Indivikar/mateCounter/fritzing/2.8 TFT SPI 240x320.png

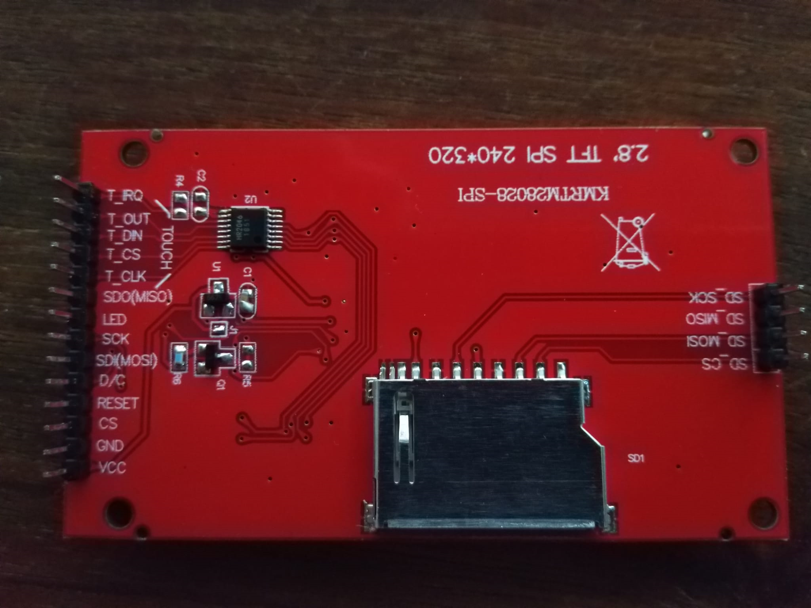
fritzing/2.8 TFT SPI 240x320.png
